computerguy096/ModularAT/documentation/diagrams/base.jpg

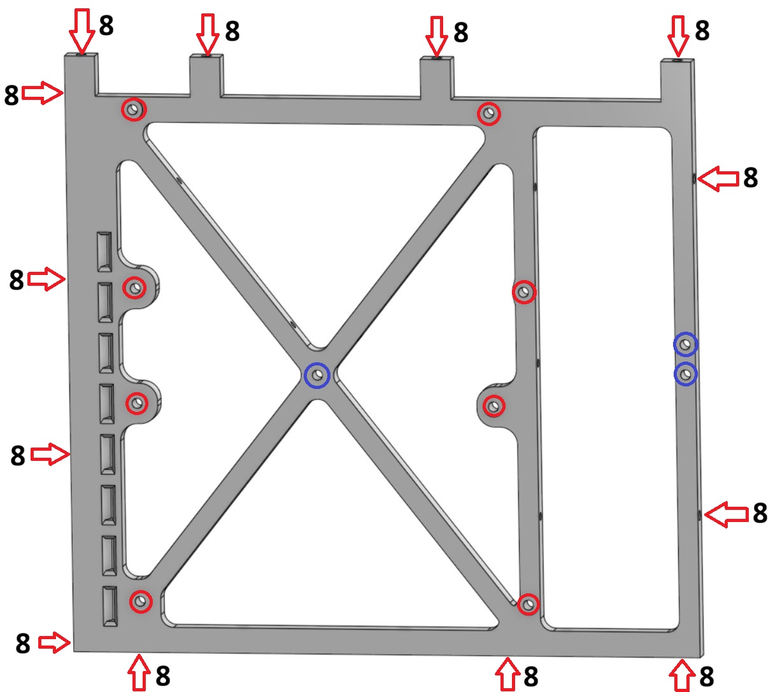
documentation/diagrams/base.jpg
