computerguy096/ModularAT/documentation/diagrams/base_ext.jpg

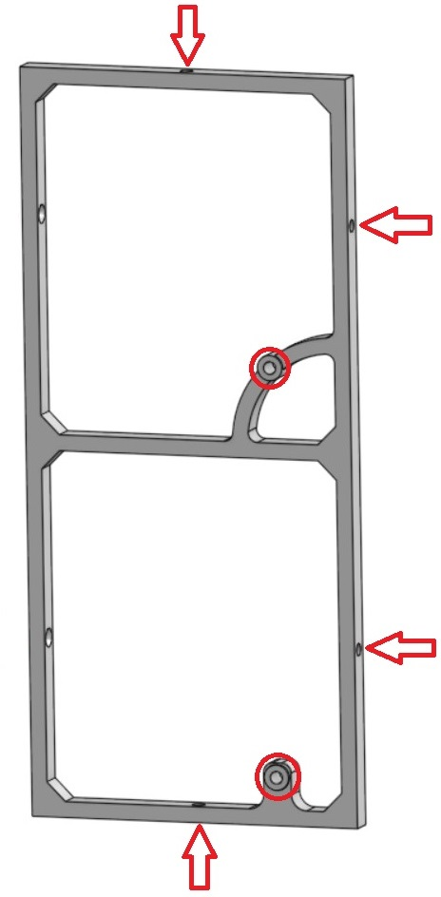
documentation/diagrams/base_ext.jpg
