computerguy096/ModularAT/documentation/diagrams/bottom.jpg

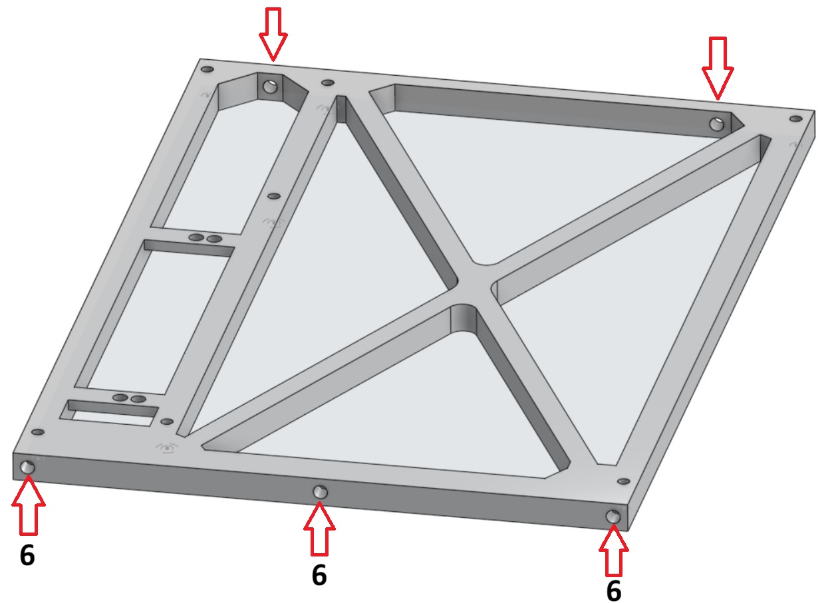
documentation/diagrams/bottom.jpg
