computerguy096/ModularAT/documentation/diagrams/bottom_ext.jpg

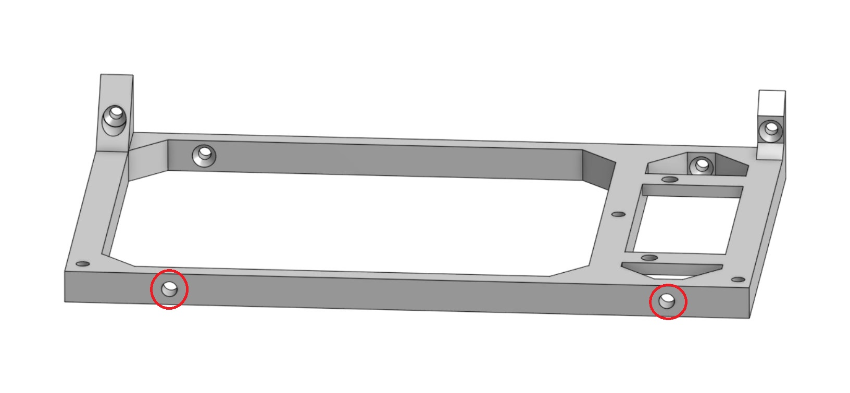
documentation/diagrams/bottom_ext.jpg
