computerguy096/ModularAT/documentation/diagrams/front.jpg

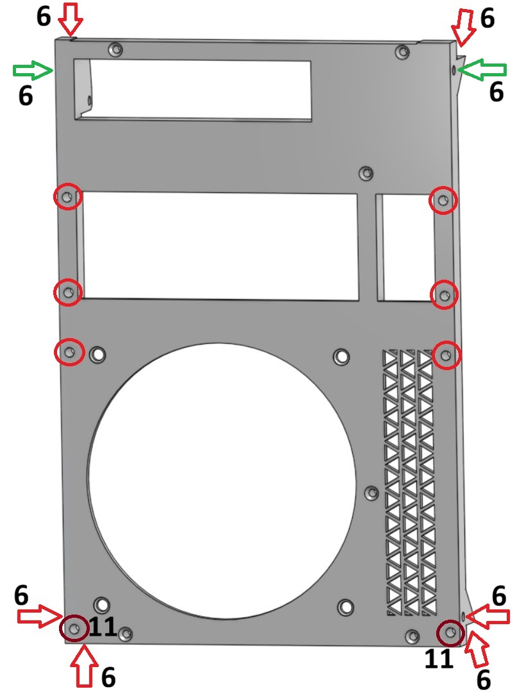
documentation/diagrams/front.jpg
