computerguy096/ModularAT/documentation/diagrams/middle.jpg

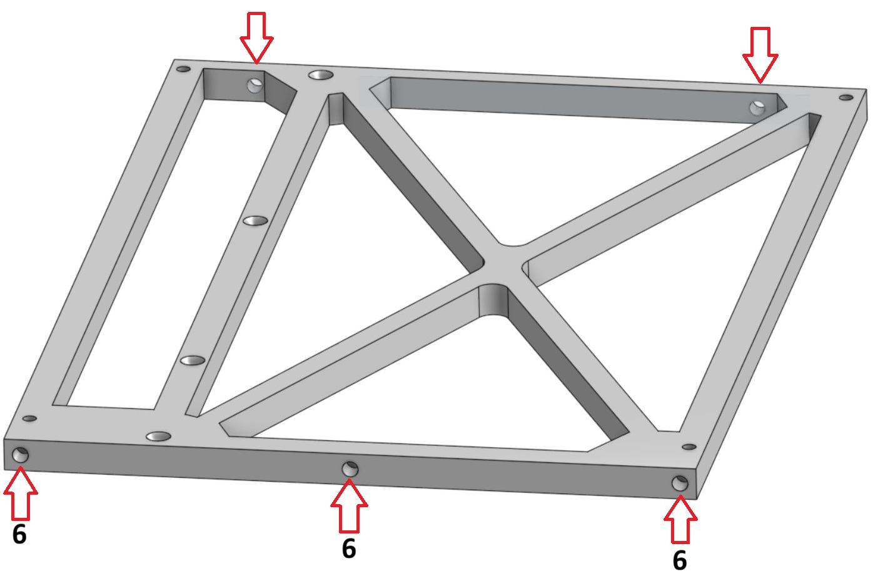
documentation/diagrams/middle.jpg
