computerguy096/ModularAT/documentation/diagrams/middle_ext.jpg

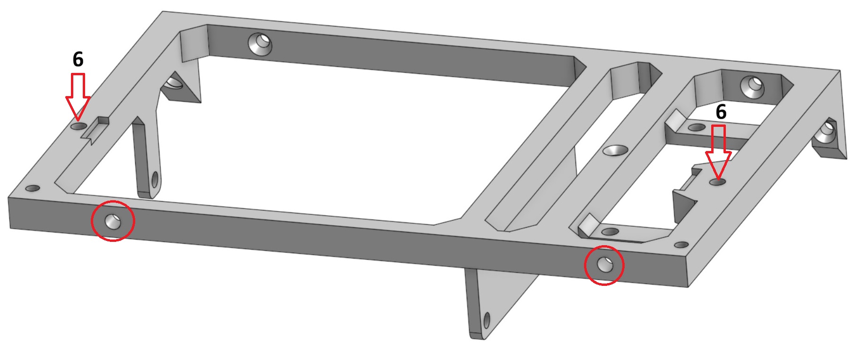
documentation/diagrams/middle_ext.jpg
