computerguy096/ModularAT/documentation/diagrams/psu.jpg

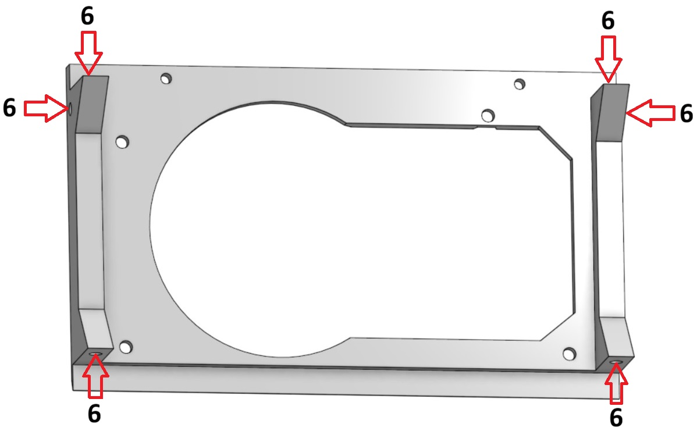
documentation/diagrams/psu.jpg
