computerguy096/ModularAT/documentation/diagrams/rear.jpg

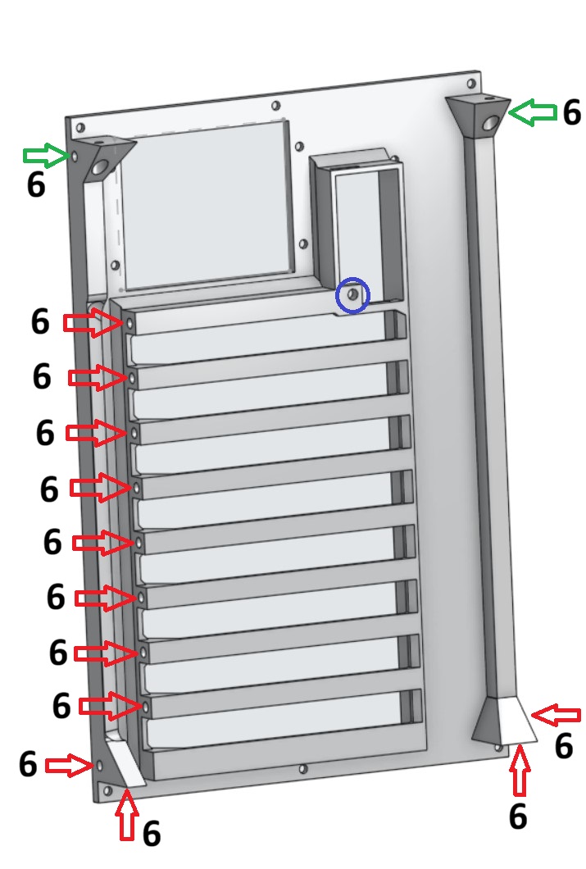
documentation/diagrams/rear.jpg
