computerguy096/ModularAT/documentation/diagrams/stability.jpg

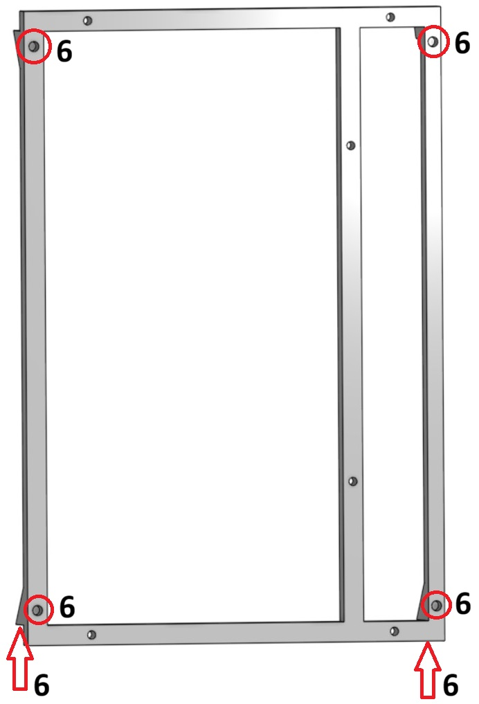
documentation/diagrams/stability.jpg
