computerguy096/ModularAT/documentation/diagrams/top.jpg

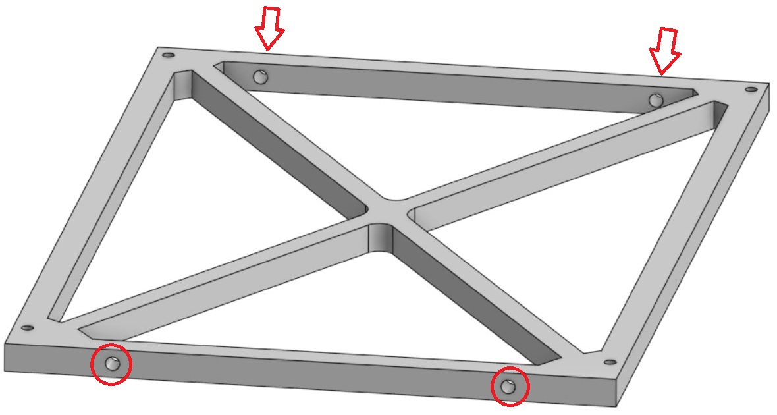
documentation/diagrams/top.jpg
