computerguy096/ModularAT/documentation/diagrams/top_ext.jpg

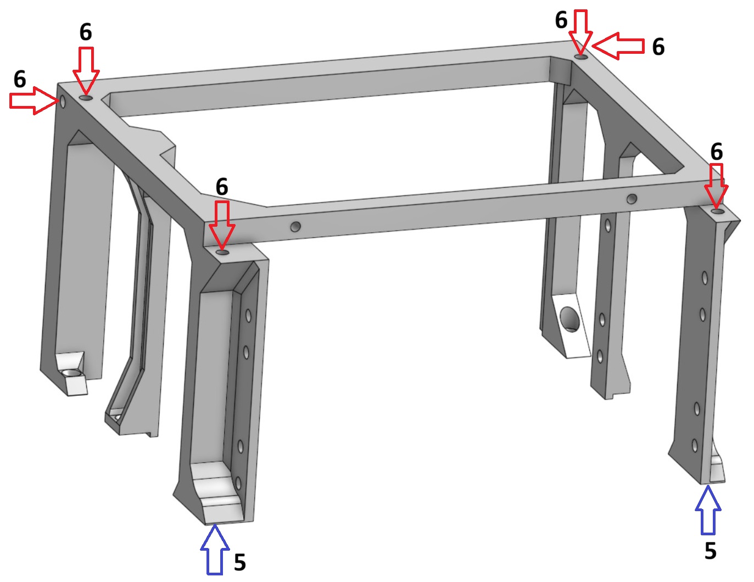
documentation/diagrams/top_ext.jpg
