computerguy096/ModularAT/images/rear.jpg

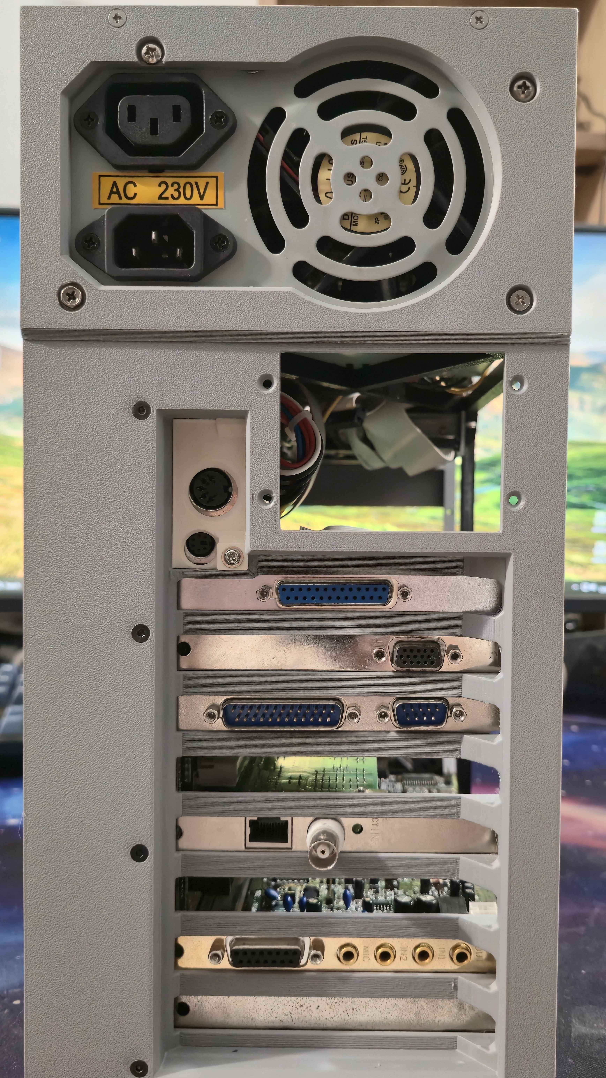
images/rear.jpg
