computerguy096/ModularAT/images/side1.jpg

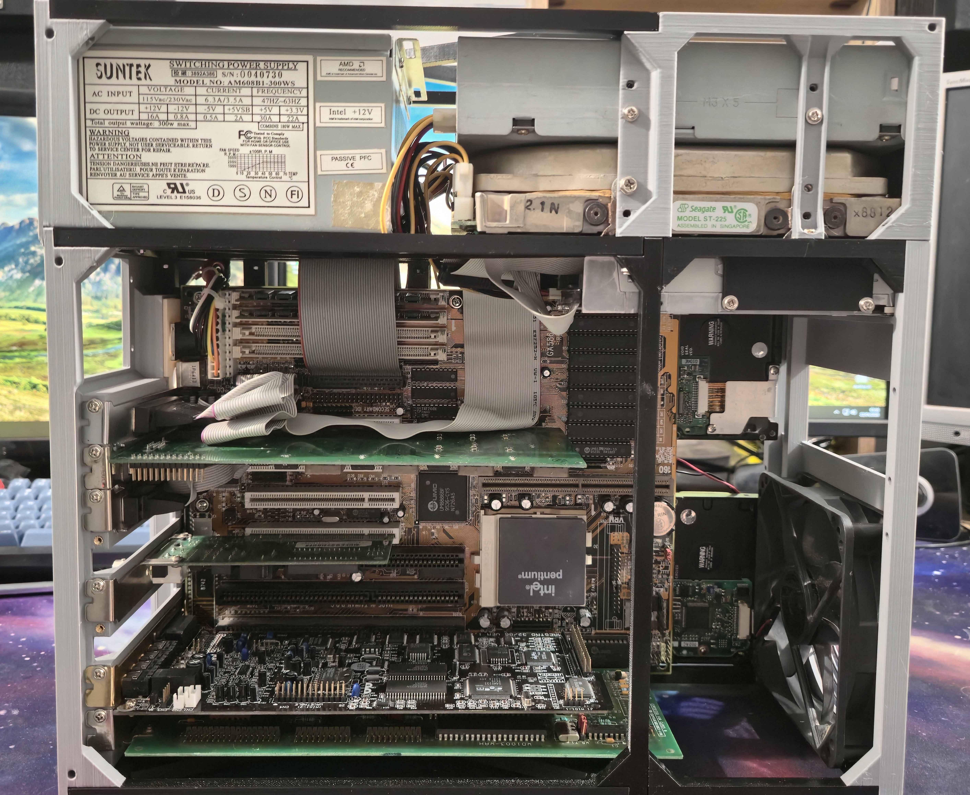
images/side1.jpg
