computerguy096/ModularAT/STL/accessories/HDD holder rear.stl

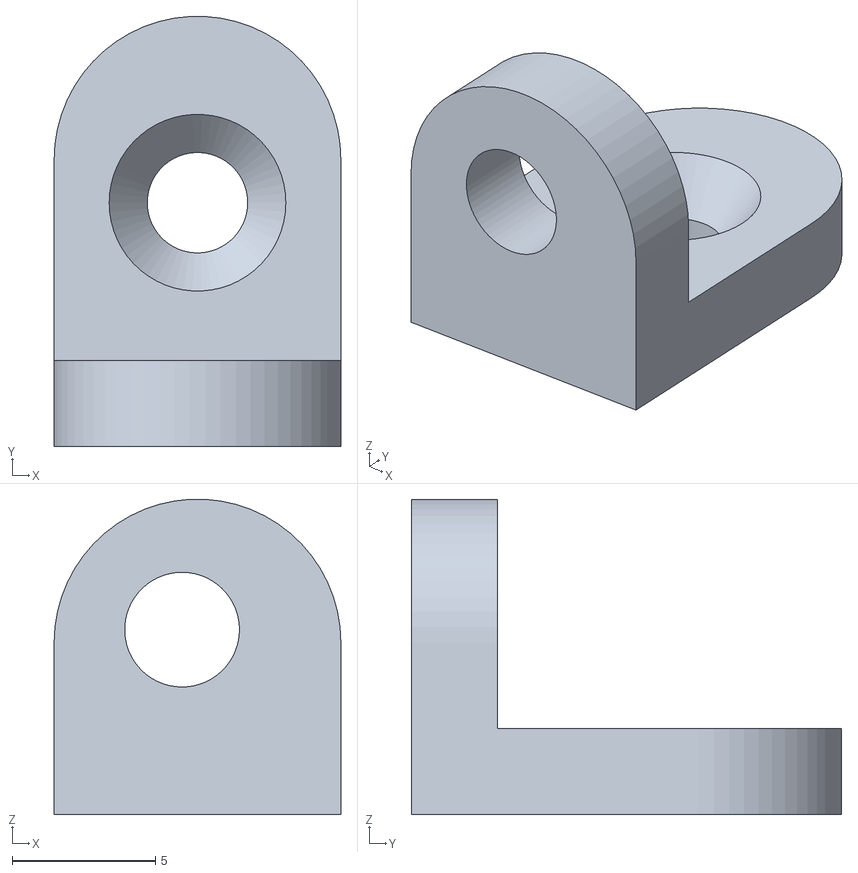
[picture p33: CAD file, 2026-04-24]
STL/accessories/HDD holder rear.stl
10.0 x 15.0 x 11.0
