computerguy096/ModularAT/STL/frame/Bottom frame.stl

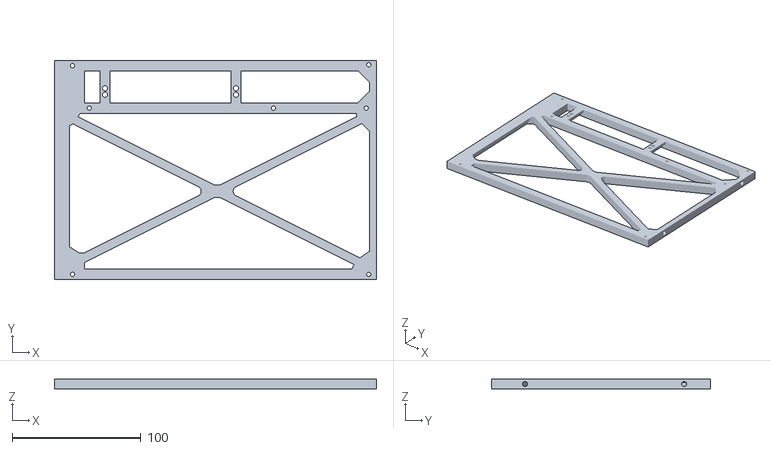
[picture p34: CAD file, 2026-04-24]
STL/frame/Bottom frame.stl
250.0 x 170.0 x 8.00
