computerguy096/ModularAT/STL/accessories/KB cover - blank.stl

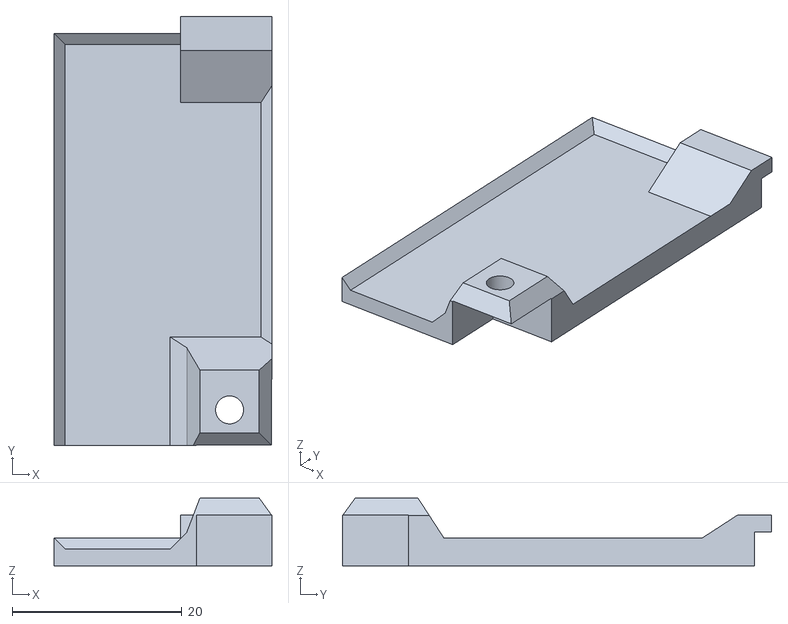
[picture p35: CAD file, 2026-04-24]
STL/accessories/KB cover - blank.stl
25.7 x 50.6 x 8.00
