computerguy096/ModularAT/STL/frame/Base frame.stl

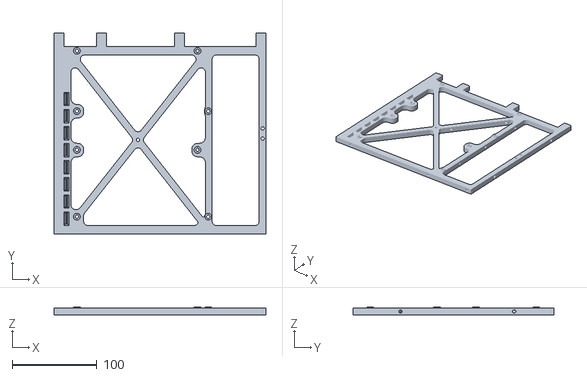
[picture p36: CAD file, 2026-04-24]
STL/frame/Base frame.stl
250.0 x 237.0 x 9.00
