computerguy096/ModularAT/STL/frame/Middle frame.stl

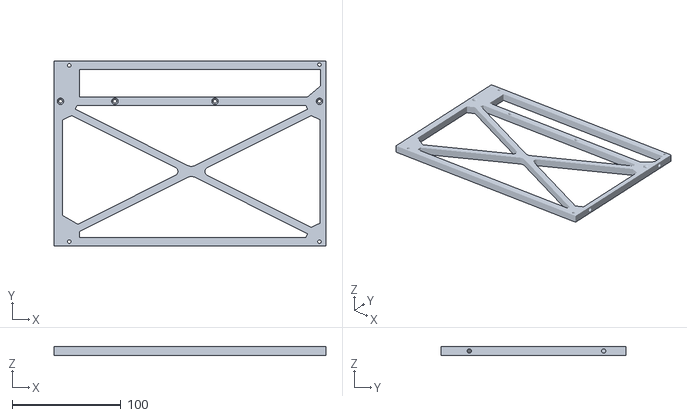
[picture p37: CAD file, 2026-04-24]
STL/frame/Middle frame.stl
250.0 x 170.0 x 8.00
