computerguy096/ModularAT/STL/frame/Base extension frame.stl

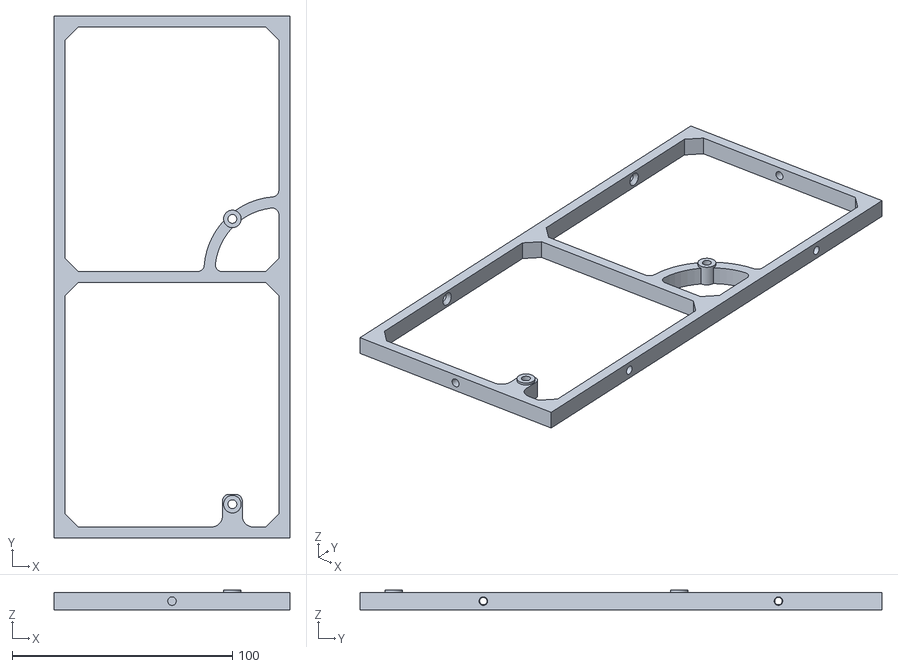
[picture p38: CAD file, 2026-04-24]
STL/frame/Base extension frame.stl
107.0 x 237.0 x 9.00
