computerguy096/ModularAT/documentation/diagrams/step3.jpg

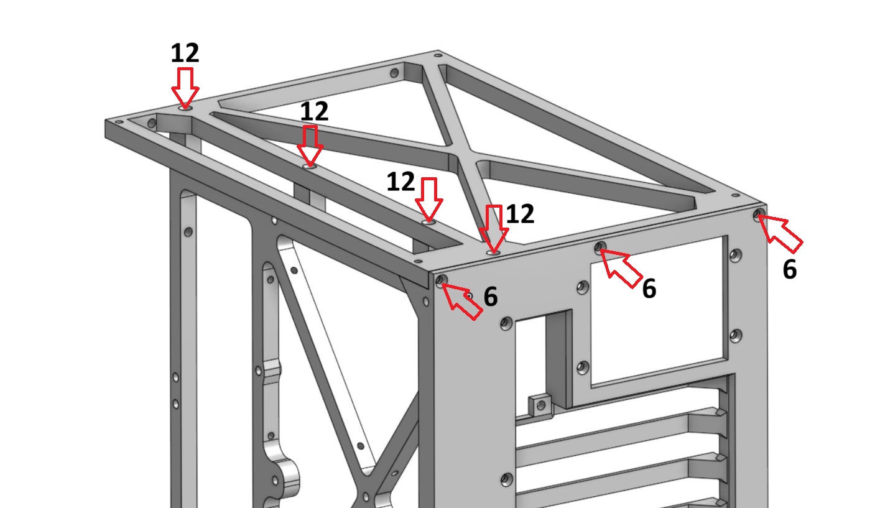
documentation/diagrams/step3.jpg
