computerguy096/ModularAT/documentation/diagrams/step6.jpg

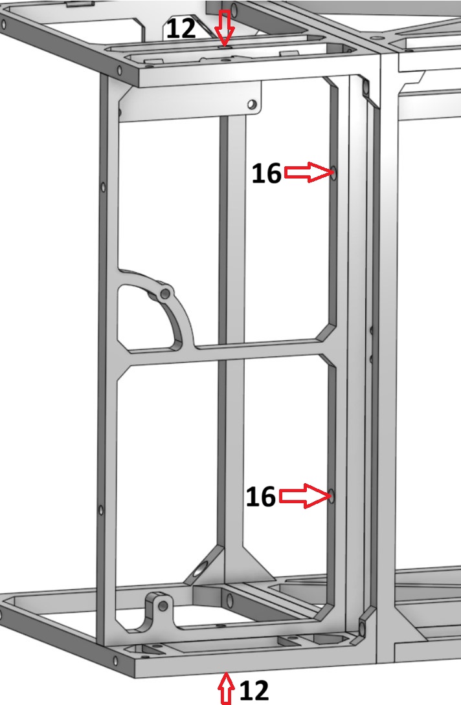
documentation/diagrams/step6.jpg
