computerguy096/ModularAT/documentation/diagrams/step8a.jpg

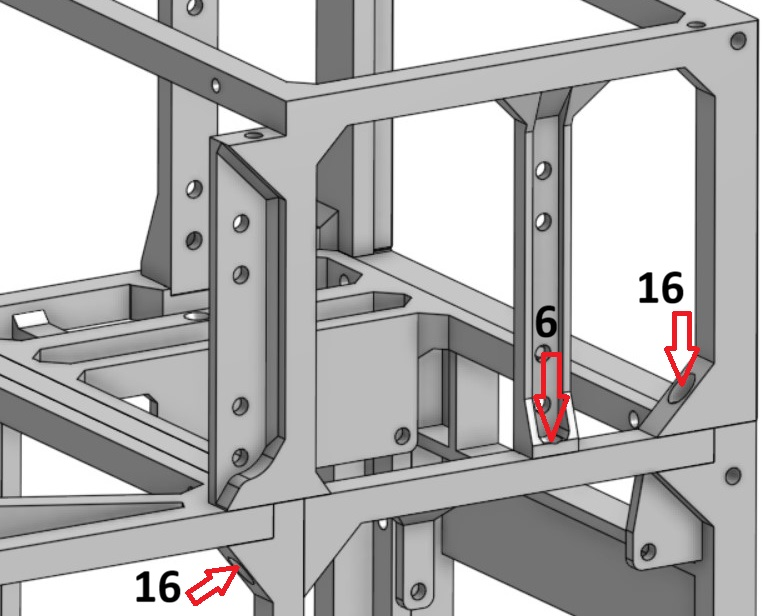
documentation/diagrams/step8a.jpg
