computerguy096/ModularAT/images/side2.jpg

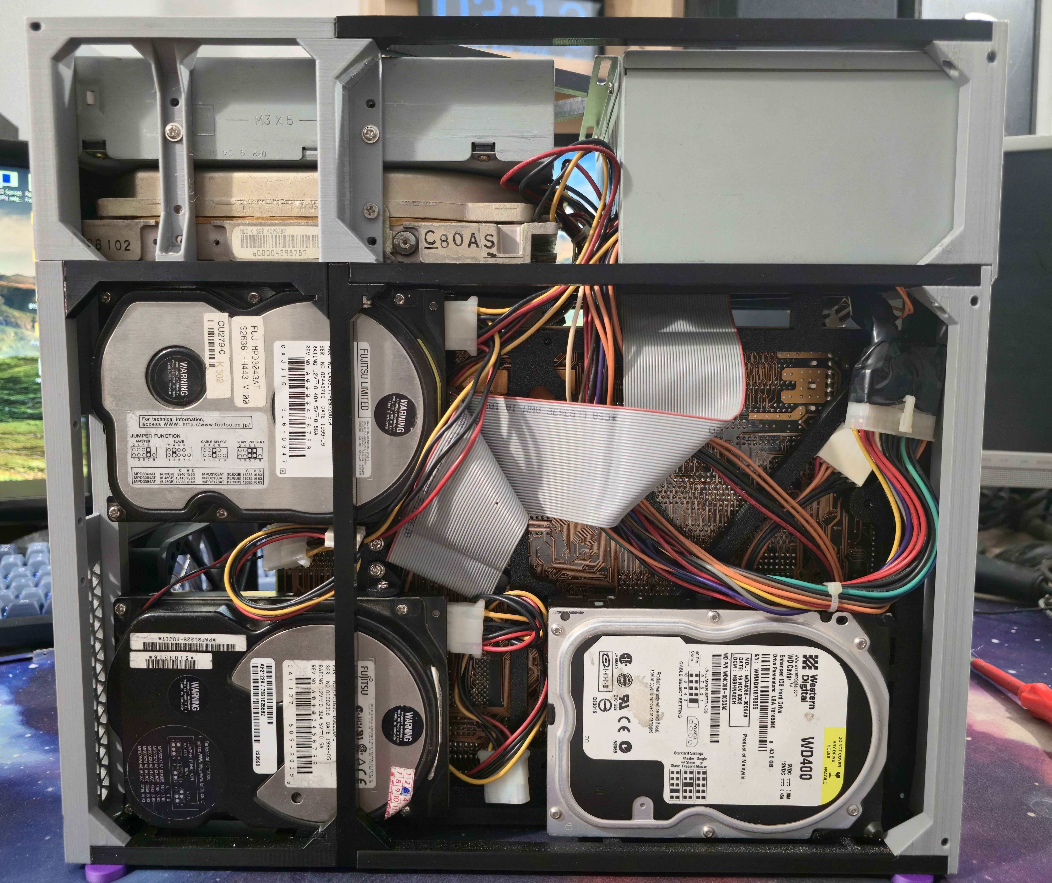
images/side2.jpg
